limpkin/cdm324_fft/fw/Core/Src/user/clocks.c

#include "user/clocks.h"


/*! \fn     clocks_init(void)
*   \brief  Clocks initialization code
*/
void clocks_init(void)
{
	RCC_OscInitTypeDef RCC_OscInitStruct = {0};
	RCC_ClkInitTypeDef RCC_ClkInitStruct = {0};
	RCC_PeriphCLKInitTypeDef PeriphClkInit = {0};

	__HAL_RCC_SYSCFG_CLK_ENABLE();
	__HAL_RCC_PWR_CLK_ENABLE();

	RCC_OscInitStruct.OscillatorType = RCC_OSCILLATORTYPE_HSI;
	RCC_OscInitStruct.HSIState = RCC_HSI_ON;
	RCC_OscInitStruct.HSICalibrationValue = RCC_HSICALIBRATION_DEFAULT;
	RCC_OscInitStruct.PLL.PLLState = RCC_PLL_ON;
	RCC_OscInitStruct.PLL.PLLSource = RCC_PLLSOURCE_HSI;
	RCC_OscInitStruct.PLL.PLLMUL = RCC_PLL_MUL16;
	HAL_RCC_OscConfig(&RCC_OscInitStruct);

	RCC_ClkInitStruct.ClockType = RCC_CLOCKTYPE_HCLK|RCC_CLOCKTYPE_SYSCLK|RCC_CLOCKTYPE_PCLK1|RCC_CLOCKTYPE_PCLK2;
	RCC_ClkInitStruct.SYSCLKSource = RCC_SYSCLKSOURCE_PLLCLK;
	RCC_ClkInitStruct.AHBCLKDivider = RCC_SYSCLK_DIV1;
	RCC_ClkInitStruct.APB1CLKDivider = RCC_HCLK_DIV2;
	RCC_ClkInitStruct.APB2CLKDivider = RCC_HCLK_DIV1;
	HAL_RCC_ClockConfig(&RCC_ClkInitStruct, FLASH_LATENCY_2);

	PeriphClkInit.PeriphClockSelection = RCC_PERIPHCLK_ADC1;
	PeriphClkInit.Adc1ClockSelection = RCC_ADC1PLLCLK_DIV128;
	PeriphClkInit.I2c1ClockSelection = RCC_I2C1CLKSOURCE_HSI;
	HAL_RCCEx_PeriphCLKConfig(&PeriphClkInit);
}
